jfm92/microByte_PCB/components_3d/micro-Byte_front0.png

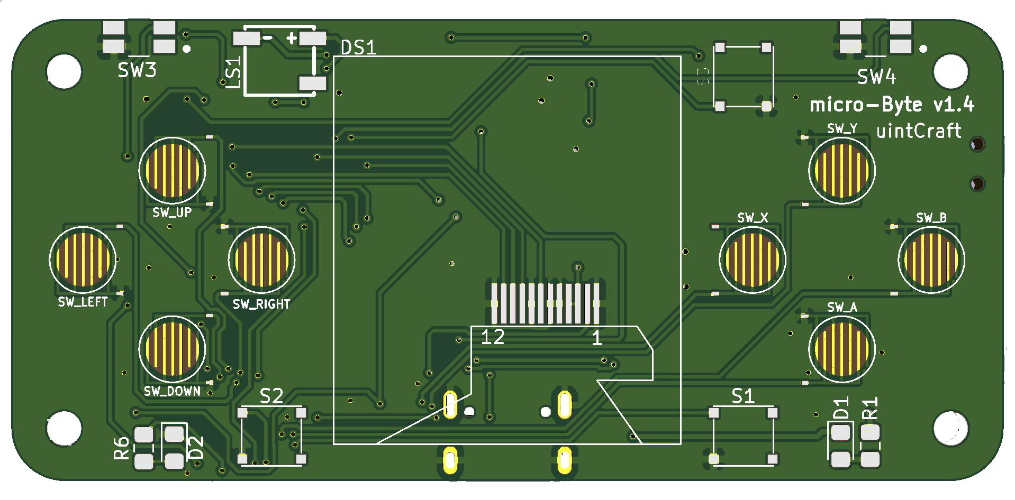
components_3d/micro-Byte_front0.png
